DF4IAH/DL0WH_BiTuner/CAD/Eagle/Manufacturing/Pictures/HW_1V0/Bottom.png

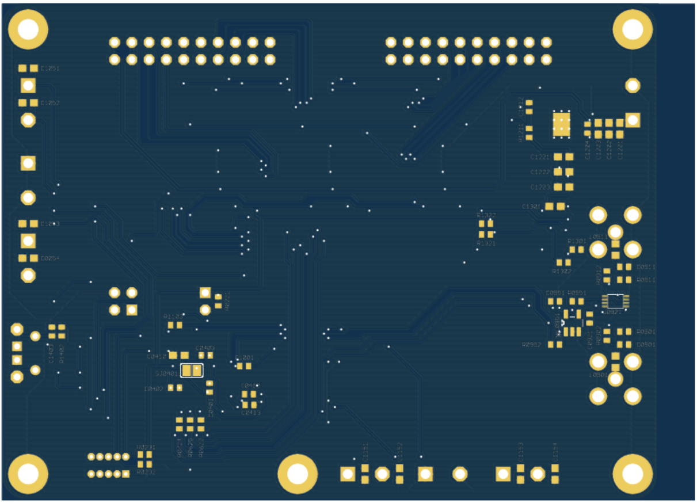
CAD/Eagle/Manufacturing/Pictures/HW_1V0/Bottom.png
