DF4IAH/DL0WH_BiTuner/CAD/Eagle/Manufacturing/Pictures/HW_1V0/Top_Silkscreen.png

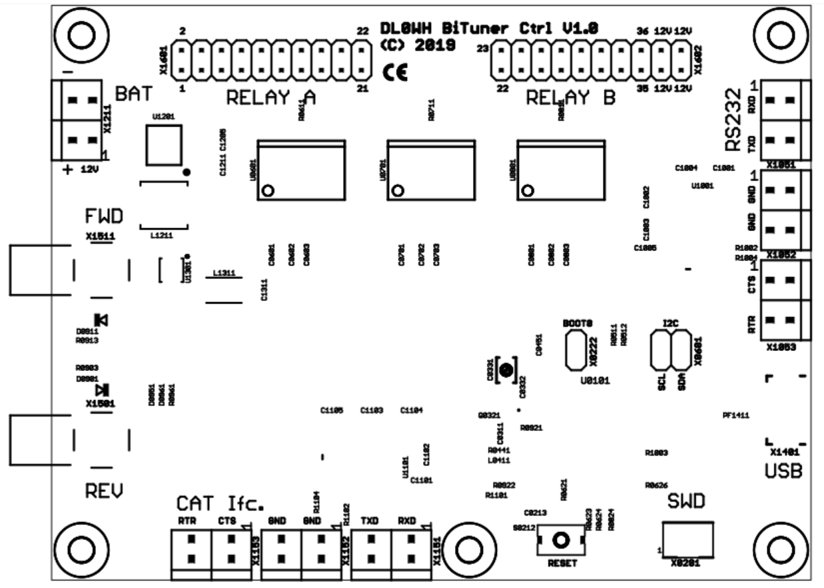
CAD/Eagle/Manufacturing/Pictures/HW_1V0/Top_Silkscreen.png
