DF4IAH/DL0WH_BiTuner/CAD/Eagle/Manufacturing/Pictures/HW_1V1/Bottom.png

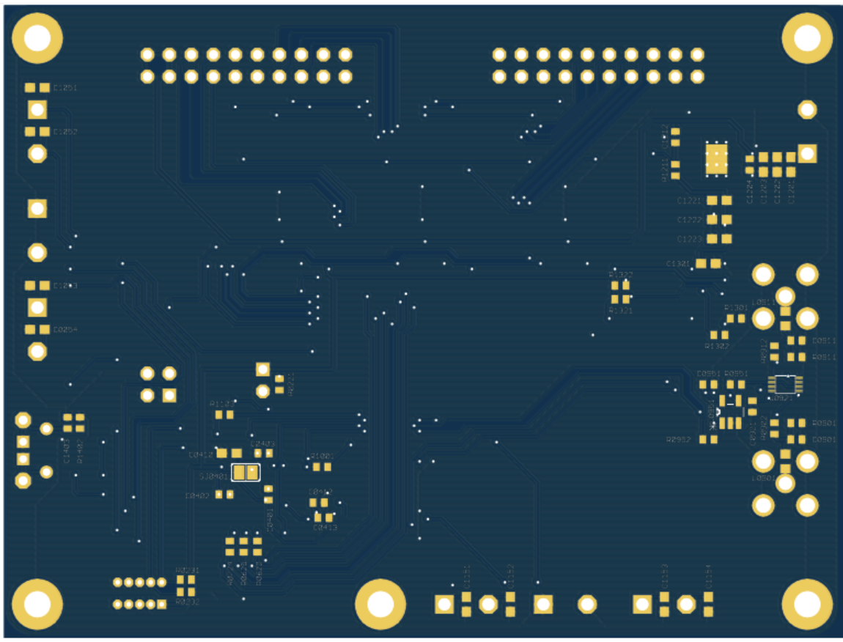
CAD/Eagle/Manufacturing/Pictures/HW_1V1/Bottom.png
