DF4IAH/DL0WH_BiTuner/CAD/Eagle/Manufacturing/Pictures/HW_1V1/Top.png

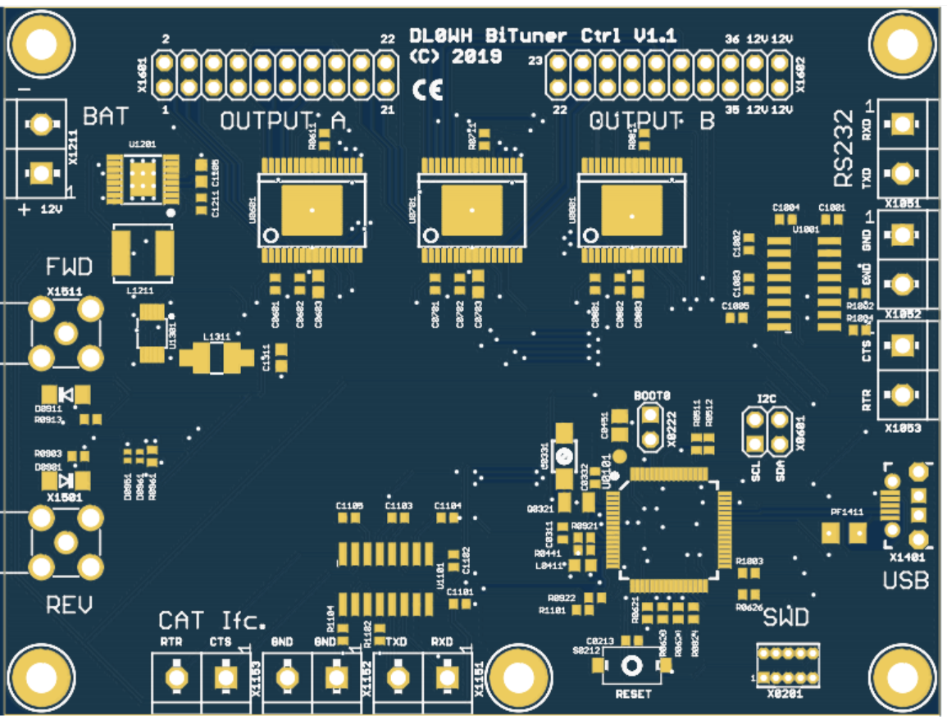
CAD/Eagle/Manufacturing/Pictures/HW_1V1/Top.png
