DF4IAH/DL0WH_BiTuner/Docs/09_Results/DL0WH_BiTuner_1V2_Rework_of_LogAmp/BiTuner_LogAmp__10C_30C_50C__1N43_2.png

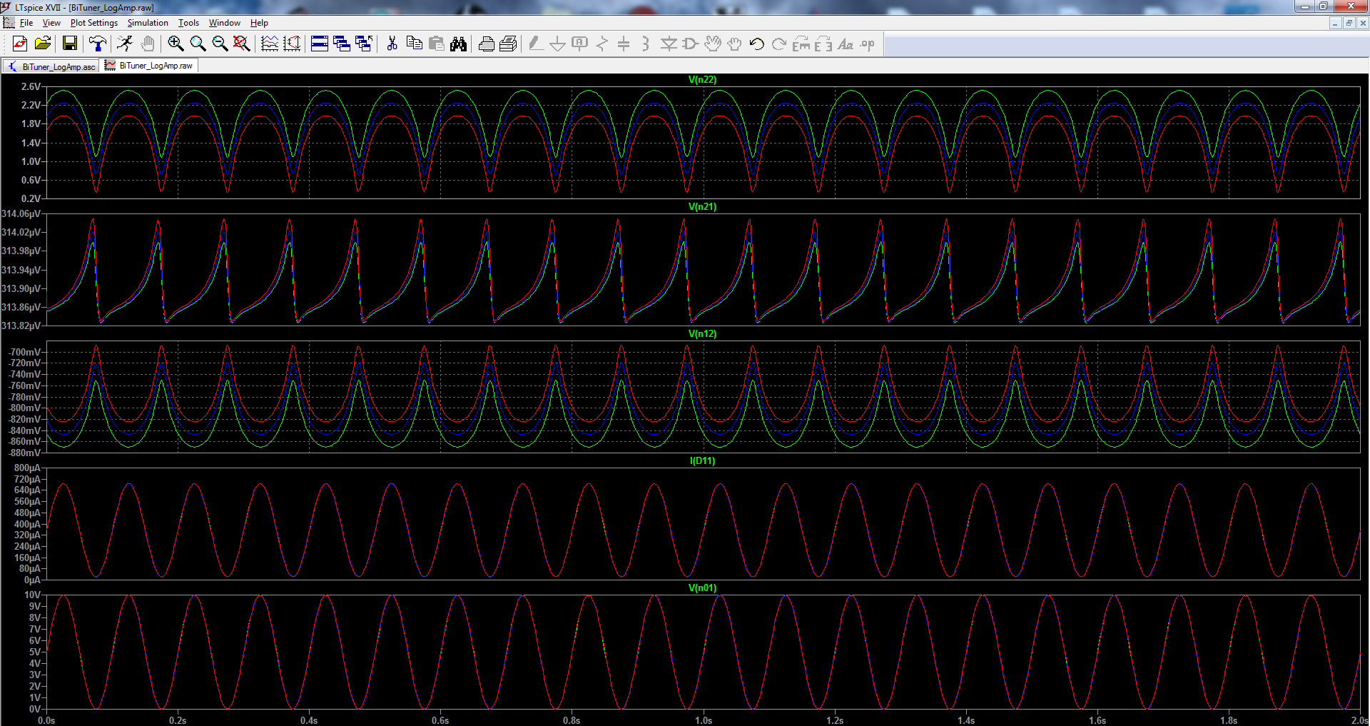
Docs/09_Results/DL0WH_BiTuner_1V2_Rework_of_LogAmp/BiTuner_LogAmp__10C_30C_50C__1N43_2.png
