DF4IAH/DL0WH_BiTuner/Docs/09_Results/Pictures/DL0WH_BiTuner_1V0_PCB_RoutingDone.png

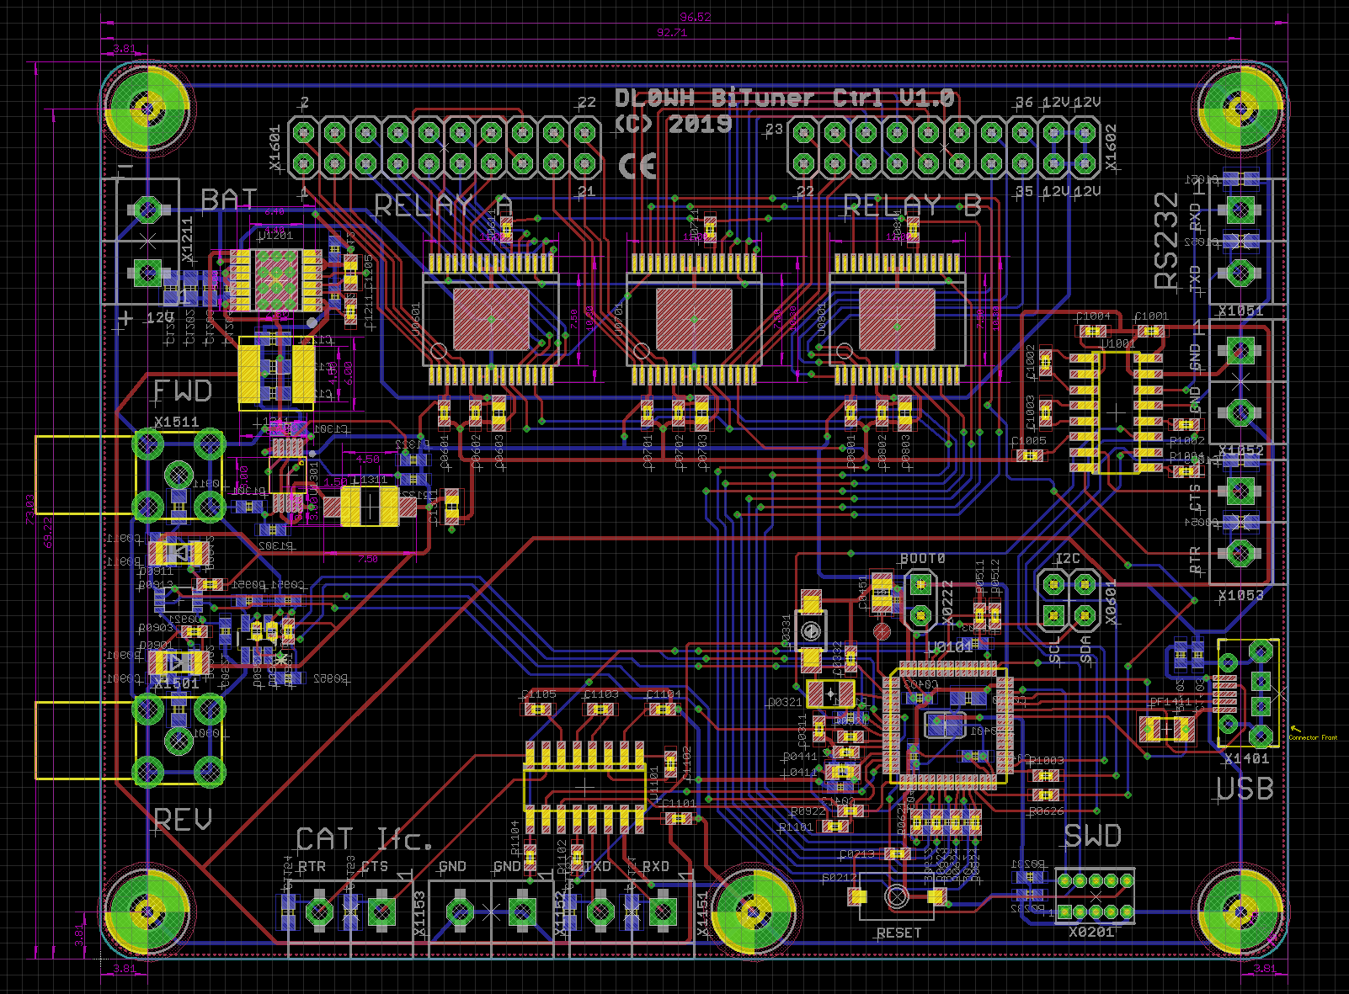
Docs/09_Results/Pictures/DL0WH_BiTuner_1V0_PCB_RoutingDone.png
