DF4IAH/DL0WH_BiTuner/Docs/09_Results/DL0WH_BiTuner_1V2_Rework_of_LogAmp/BiTuner_LogAmp.asc

C22: cap; 100pF
D11: diode; CMAD6001
R1: res; 150kR
R2: res; 2kR
R4: res; 1kR
R11: res; 15kR
R12: res; 1kR
R21: res; 5.3kR
R22: res; 20kR
U1: OPA354
U2: OPA354
V1: voltage; 3.3V
V2: voltage; 1.5V
V3: voltage; SINE(5 5 10)
Named nets: 0, n11, n12, n21, n22, nVp, nVm, n05, n01
.tran 0 2 0
*.step temp 10 50 20
.model CMAD6001 D( IS=70.1f RS=0.658 BV=75.0 IBV=500p CJO=2.00p M=0.333 N=1.24 TT=4.32u mfg=Central type=silicon )
