DF4IAH/DL0WH_BiTuner/Docs/09_Results/DL0WH_BiTuner_1V2_Rework_of_LogAmp/BiTuner_TempDiode.asc

D11: diode; CMAD6001
R1: res; 10kR
V1: voltage; 3.3V
Named nets: 0, nVp, nDa
.step temp 10 50 20
.tran 0 1 0
.model CMAD6001 D( IS=70.1f RS=0.658 BV=75.0 IBV=500p CJO=2.00p M=0.333 N=1.24 TT=4.32u mfg=Central type=silicon )
