DF4IAH/DL0WH_BiTuner/SW/_historic/DL0WH_BiTuner_Firmware/src/driver_init.c

/**
 * \file
 *
 * \brief Driver initialization.
 *
 (c) 2018 Microchip Technology Inc. and its subsidiaries.

    Subject to your compliance with these terms,you may use this software and
    any derivatives exclusively with Microchip products.It is your responsibility
    to comply with third party license terms applicable to your use of third party
    software (including open source software) that may accompany Microchip software.

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
    IN NO EVENT WILL MICROCHIP BE LIABLE FOR ANY INDIRECT, SPECIAL, PUNITIVE,
    INCIDENTAL OR CONSEQUENTIAL LOSS, DAMAGE, COST OR EXPENSE OF ANY KIND
    WHATSOEVER RELATED TO THE SOFTWARE, HOWEVER CAUSED, EVEN IF MICROCHIP HAS
    BEEN ADVISED OF THE POSSIBILITY OR THE DAMAGES ARE FORESEEABLE. TO THE
    FULLEST EXTENT ALLOWED BY LAW, MICROCHIP'S TOTAL LIABILITY ON ALL CLAIMS IN
    ANY WAY RELATED TO THIS SOFTWARE WILL NOT EXCEED THE AMOUNT OF FEES, IF ANY,
    THAT YOU HAVE PAID DIRECTLY TO MICROCHIP FOR THIS SOFTWARE.
 *
 */

/*
 * Code generated by START.
 *
 * This file will be overwritten when reconfiguring your START project.
 * Please copy examples or other code you want to keep to a separate file
 * to avoid losing it when reconfiguring.
 */

#include "driver_init.h"
#include <system.h>

void EXTERNAL_IRQ_0_initialization(void)
{

	EXTERNAL_IRQ_0_init();
}

/* Configure pins and initialize registers */
void ADC_0_initialization(void)
{

	ADC_0_init();
}

/* Configure pins and initialize registers */
void AC_0_initialization(void)
{

	AC_0_init();
}

/* configure pins and initialize registers */
void I2C_0_initialization(void)
{
	I2C_0_init();
}

/* configure the pins and initialize the registers */
void DAC_0_initialization(void)
{

	// Set pin direction to input
	PB4_set_dir(PORT_DIR_IN);

	PB4_set_pull_mode(
	    // <y> Pull configuration
	    // <id> pad_pull_config
	    // <PORT_PULL_OFF"> Off
	    // <PORT_PULL_UP"> Pull-up
	    PORT_PULL_OFF);

	// Set pin direction to output
	PB3_set_dir(PORT_DIR_OUT);

	PB3_set_level(
	    // <y> Initial level
	    // <id> pad_initial_level
	    // <false"> Low
	    // <true"> High
	    false);

	// Set pin direction to output
	PB5_set_dir(PORT_DIR_OUT);

	PB5_set_level(
	    // <y> Initial level
	    // <id> pad_initial_level
	    // <false"> Low
	    // <true"> High
	    false);

	DAC_0_init();
}

void PWM_0_initialization(void)
{

	PWM_0_init();
}

void PWM_1_initialization(void)
{

	PWM_1_init();
}

void TIMER_0_initialization(void)
{

	TIMER_0_init();
}

/* configure pins and initialize registers */
void USART_0_initialization(void)
{

	// Set pin direction to input
	PD0_set_dir(PORT_DIR_IN);

	PD0_set_pull_mode(
	    // <y> Pull configuration
	    // <id> pad_pull_config
	    // <PORT_PULL_OFF"> Off
	    // <PORT_PULL_UP"> Pull-up
	    PORT_PULL_OFF);

	// Set pin direction to output
	PD1_set_dir(PORT_DIR_OUT);

	PD1_set_level(
	    // <y> Initial level
	    // <id> pad_initial_level
	    // <false"> Low
	    // <true"> High
	    false);

	USART_0_init();
}

/**
 * \brief System initialization
 */
void system_init()
{
	mcu_init();

	sysctrl_init();

	FLASH_0_init();

	WDT_0_init();

	EXTERNAL_IRQ_0_initialization();

	//ADC_0_initialization();

	//AC_0_initialization();

	//I2C_0_initialization();

	//DAC_0_initialization();

	//PWM_0_initialization();

	//PWM_1_initialization();

	TIMER_0_initialization();

	/* GPIO init */
	{	
		//PORTB_set_port_dir(0xc0, PORT_DIR_IN);
		PORTB_set_port_dir(0x07, PORT_DIR_OUT);
		PORTB_write_port(0x00);

		//PORTC_set_port_dir(0xc0, PORT_DIR_IN);
		PORTC_set_port_dir(0x3f, PORT_DIR_OUT);
		PORTC_write_port(0x02);

		//PORTD_set_port_dir(0x01, PORT_DIR_IN);
		PORTD_set_port_dir(0xfc, PORT_DIR_OUT);
		PORTD_write_port(0x00);
	}

	USART_0_initialization();
}
