DF4IAH/DL0WH_BiTuner/SW/_Tests/prove.c

#include <stdio.h>
#include <string.h>
#include <stdlib.h>
#include <math.h>
#include "complex.h"

#include "prove.h"


extern float                g_adc_fwd_mv;
extern float                g_adc_swr;


static const float Controller_L0_nH                           = 50.0f;
static const float Controller_Ls_nH[8]                        = {
    187.5f,
    375.0f,
    750.0f,
    1.5e+3f,
    3.0e+3f,
    6.0e+3f,
    12.0e+3f,
    24.0e+3f
};

static const float Controller_C0_pF                           = 25.0f;
static float Controller_Cs_pF[8]                              = {
    25.0f,
    //33.0f,
    50.0f,
    89.0f,
    165.0f,
    340.0f,
    600.0f,
    1137.0f,
    1939.0f
};

static const float            Controller_AutoSWR_P_mW_Min       = 5.0f;
static const float            Controller_AutoSWR_P_mW_Max       = 15.0f;
static const float            Controller_AutoSWR_SWR_Max        = 1.1f;
static const float            Controller_AutoSWR_Time_ms_Max    = 750.0f;
static const uint8_t          Controller_AutoSWR_CVHpong_Max    = 3U;
static const uint8_t          Controller_AutoSWR_LCpong_Max     = 5U;
static uint32_t               s_controller_swr_tmr              = 0UL;
static uint32_t               s_controller_30ms_cnt             = 0UL;

static ControllerFsm_t        s_controller_FSM_state            = ControllerFsm__NOP;
static ControllerOptiCVH_t    s_controller_FSM_optiCVH          = ControllerOptiCVH__CV;
static ControllerOptiLC_t     s_controller_FSM_optiLC           = ControllerOptiLC__L;
static ControllerOptiStrat_t  s_controller_FSM_optiStrat        = ControllerOptiStrat__Double;
static ControllerOptiUpDn_t   s_controller_FSM_optiUpDn         = ControllerOptiUpDn__Up;
static uint8_t                s_controller_opti_CVHpongCtr      = 0U;
static uint8_t                s_controller_opti_LCpongCtr       = 0U;
static float                  s_controller_opti_min_swr         = 0.0f;
static float                  s_controller_opti_min_cand_swr    = 0.0f;
static float                  s_controller_opti_mid_swr         = 0.0f;
static float                  s_controller_opti_max_cand_swr    = 0.0f;
static float                  s_controller_opti_max_swr         = 0.0f;
static uint8_t                s_controller_opti_L               = 0U;
static float                  s_controller_opti_L_min_val       = 0.0f;
static float                  s_controller_opti_L_min_cand_val  = 0.0f;
static float                  s_controller_opti_L_mid_val       = 0.0f;
static float                  s_controller_opti_L_max_cand_val  = 0.0f;
static float                  s_controller_opti_L_max_val       = 0.0f;
static uint8_t                s_controller_opti_C               = 0U;
static float                  s_controller_opti_C_min_val       = 0.0f;
static float                  s_controller_opti_C_min_cand_val  = 0.0f;
static float                  s_controller_opti_C_mid_val       = 0.0f;
static float                  s_controller_opti_C_max_cand_val  = 0.0f;
static float                  s_controller_opti_C_max_val       = 0.0f;

static float                  s_controller_adc_fwd_mv           = 0.0f;
static float                  s_controller_adc_swr              = 0.0f;
static float                  s_controller_adc_fwd_mw           = 0.0f;
static float                  s_controller_last_swr             = 0.0f;

static _Bool                  s_controller_doCycle              = false;
static _Bool                  s_controller_doAdc                = false;



uint32_t controllerCalcMsgHdr(ControllerMsgDestinations_t dst, ControllerMsgDestinations_t src, uint8_t lengthBytes, uint8_t cmd)
{
  return ((uint32_t)dst << 24U) | ((uint32_t)src << 16U) | ((uint32_t)lengthBytes << 8U) | ((uint32_t)cmd);
}

uint32_t controllerCalcMsgInit(uint32_t* ary, ControllerMsgDestinations_t dst, uint32_t startDelayMs)
{
  ary[0] = 0; // controllerCalcMsgHdr(dst, Destinations__Controller, sizeof(uint32_t), MsgController__InitDo);
  ary[1] = startDelayMs;
  return 2UL;
}


/* Calculation function */

float controllerCalcMatcherL2nH(uint8_t Lval)
{
  float sum = Controller_L0_nH;

  for (uint8_t idx = 0; idx < 8; idx++) {
    if (Lval & (1U << idx)) {
      sum += Controller_Ls_nH[idx];
    }
  }
  return sum;
}

float controllerCalcMatcherC2pF(uint8_t Cval)
{
  float sum = Controller_C0_pF;

  for (uint8_t idx = 0; idx < 8; idx++) {
    if (Cval & (1U << idx)) {
      sum += Controller_Cs_pF[idx];
    }
  }
  return sum;
}

uint8_t controllerCalcMatcherNH2L(float nH)
{
  float   absMin  = 1e+3f;
  uint8_t valThis = 0U;

  for (uint16_t val = 0U; val < 256U; val++) {
    const float valL    = controllerCalcMatcherL2nH(val);
    const float absThis = fabs(valL - nH);

    if (absMin > absThis) {
      absMin  = absThis;
      valThis = val;
    }
  }
  return valThis;
}

uint8_t controllerCalcMatcherPF2C(float pF)
{
  float   absMin  = 1e+3f;
  uint8_t valThis = 0U;

  for (uint16_t val = 0U; val < 256U; val++) {
    const float valC    = controllerCalcMatcherC2pF(val);
    const float absThis = fabs(valC - pF);

    if (absMin > absThis) {
      absMin  = absThis;
      valThis = val;
    }
  }
  return valThis;
}

float controllerCalcVSWR_Simu(float antOhmR, float antOhmI, float Z0R, float Z0I, float frequencyHz)
{
  const float Z0abs = sqrtf(Z0R * Z0R + Z0I * Z0I);
  const float omega = (float) (2.0 * M_PI * frequencyHz);
  float L_nH        = s_controller_opti_L_mid_val;
  float C_pF        = s_controller_opti_C_mid_val;
  float outR        = antOhmR;
  float outX        = antOhmI;
  float gammaRe     = 0.0f;
  float gammaIm     = 0.0f;
  float gammaAbs    = 0.0f;
  float gammaPhi    = 0.0f;
  float vswr        = 99.0f;

  /* For security only */
  if (L_nH < 1.0f) {
    L_nH = Controller_L0_nH;
  }
  if (C_pF < 1.0f) {
    C_pF = Controller_C0_pF;
  }

  if (s_controller_FSM_optiCVH == ControllerOptiCVH__CV) {
    /* Inductivity at the antenna */

    /* Serial structure */
    float LOhmX = omega * (L_nH * 1e-9f);
    outX += LOhmX;

    /* Parallel structure */
    {
      /* Invert to admitance */
      float outG = 0.0f;
      float outY = 0.0f;
      cInv(&outG, &outY, outR, outX);

      /* Capacity */
      const float COhmX = -1.0f / (omega * (C_pF * 1e-12f));
      float CSimG = 0.0f;
      float CSimY = 0.0f;
      cInv(&CSimG, &CSimY, 0.0f, COhmX);

      /* Adding C parallel to the circuit */
      outY += CSimY;

      /* Revert to impedance */
      cInv(&outR, &outX, outG, outY);
    }

  } else {
    /* Capacity at the antenna */

    /* Parallel structure */
    {
      /* Invert to admitance */
      float outG = 0.0f;
      float outY = 0.0f;
      cInv(&outG, &outY, outR, outX);

      /* Capacity */
      const float COhmX = -1.0f / (omega * (C_pF * 1e-12f));
      float CSimG = 0.0f;
      float CSimY = 0.0f;
      cInv(&CSimG, &CSimY, 0.0f, COhmX);

      /* Adding C parallel to the circuit */
      outY += CSimY;

      /* Revert to impedance */
      cInv(&outR, &outX, outG, outY);
    }

    /* Serial structure */
    float LOhmX = omega * (L_nH * 1e-9f);
    outX += LOhmX;
  }

  /* Log impedance at the transceiver */
  {
    char      buf[256];
    int32_t   trxRi, trxXi;
    uint32_t  trxRf, trxXf;

    mainCalcFloat2IntFrac(outR, 3U, &trxRi, &trxRf);
    mainCalcFloat2IntFrac(outX, 3U, &trxXi, &trxXf);

    int len = sprintf(buf,
        "VSWR_Simu: Resulting Impedance at the transceiver Z= R (%3d.%03u Ohm) + jX (%3d.%03u Ohm)\t\t having L=%5d nH and C=%5d pF, ",
        trxRi, trxRf,  trxXi, trxXf,  (uint32_t)L_nH, (uint32_t)C_pF);

    usbLogLen(buf, len);
  }

  /* Calculate Gamma = (Z - 1) / (Z + 1) */
  {
    /* Normalized Impedance */
    float outRnorm = outR / Z0abs;
    float outXnorm = outX / Z0abs;

    cDiv(&gammaRe, &gammaIm, (outRnorm - 1.0f), outXnorm, (outRnorm + 1.0f), outXnorm);

    gammaAbs = sqrtf(gammaRe * gammaRe  +  gammaIm * gammaIm);
    gammaPhi = (float) ((180.0 / M_PI) * atan2(gammaIm, gammaRe));
  }

  /* Log reflection coefficient at the transceiver */
  {
    char      buf[256];
    int32_t   gammaAbsi, gammaPhii, gammaRei, gammaImi;
    uint32_t  gammaAbsf, gammaPhif, gammaRef, gammaImf;

    mainCalcFloat2IntFrac(gammaAbs, 3U, &gammaAbsi, &gammaAbsf);
    mainCalcFloat2IntFrac(gammaPhi, 3U, &gammaPhii, &gammaPhif);
    mainCalcFloat2IntFrac(gammaRe,  3U, &gammaRei,  &gammaRef);
    mainCalcFloat2IntFrac(gammaIm,  3U, &gammaImi,  &gammaImf);

    int len = sprintf(buf,
        "|Gamma|= %1d.%03u,  Phi(Gamma)= %3d.%03u having Re(Gamma)= %3d.%03u, Im(Gamma)= %3d.%03u, ",
        gammaAbsi, gammaAbsf,  gammaPhii, gammaPhif,  gammaRei, gammaRef,  gammaImi, gammaImf);

    usbLogLen(buf, len);
  }

  /* Calculate VSWR = (1 + GammaAbs) / (1 - GammaAbs) */
  if (gammaAbs < 0.99f) {
    vswr = (1.0f + gammaAbs) / (1.0f - gammaAbs);

  } else {
    vswr = 99.9f;
  }

  /* Log reflection coefficient at the transceiver */
  {
    char buf[128];
    int32_t   vswri;
    uint32_t  vswrf;

    mainCalcFloat2IntFrac(vswr, 3U, &vswri, &vswrf);

    int len = sprintf(buf,
        "VSWR= %d.%03u.\r\n\r\n",
        vswri, vswrf);

    usbLogLen(buf, len);
  }

  return vswr;
}


/* FSM functions */

static void controllerFSM_LogAutoFinished(void)
{
  /* SWR: we have got it */

  s_controller_FSM_state = ControllerFsm__done;
  s_controller_doAdc     = true;

  /* Logging */
  {
    char buf[128];

    const int len = sprintf(buf, "Controller FSM: ControllerFsm__findImagZeroL - SWR good enough - tuner has finished.\r\n");
    usbLogLen(buf, len);
  }
}

static void controllerFSM_LogState(void)
{
  /* Show current state of optimization */
  char      buf[512];

  int32_t   s_controller_opti_L_min_val_i;
  uint32_t  s_controller_opti_L_min_val_f;

  int32_t   s_controller_opti_L_min_cand_val_i;
  uint32_t  s_controller_opti_L_min_cand_val_f;

  int32_t   s_controller_opti_L_mid_val_i;
  uint32_t  s_controller_opti_L_mid_val_f;

  int32_t   s_controller_opti_L_max_cand_val_i;
  uint32_t  s_controller_opti_L_max_cand_val_f;

  int32_t   s_controller_opti_L_max_val_i;
  uint32_t  s_controller_opti_L_max_val_f;


  int32_t   s_controller_opti_C_min_val_i;
  uint32_t  s_controller_opti_C_min_val_f;

  int32_t   s_controller_opti_C_min_cand_val_i;
  uint32_t  s_controller_opti_C_min_cand_val_f;

  int32_t   s_controller_opti_C_mid_val_i;
  uint32_t  s_controller_opti_C_mid_val_f;

  int32_t   s_controller_opti_C_max_cand_val_i;
  uint32_t  s_controller_opti_C_max_cand_val_f;

  int32_t   s_controller_opti_C_max_val_i;
  uint32_t  s_controller_opti_C_max_val_f;

  int       len;

  s_controller_30ms_cnt += 30UL;

  len = sprintf(buf,
                "Controller FSM:\tcontrollerFSM_LogState - time= %6d ms - FSM_state= %u, FSM_optiLC= %u, FSM_optiUpDn= %u, FSM_optiVCH= %u, FSM_opti_L= %03u, FSM_opti_C= %03u,\r\n" \
                "\t\t\topti_CVHpongCtr= %03u, opti_LCpongCtr= %03u,\r\n",
                s_controller_30ms_cnt,
                s_controller_FSM_state,       s_controller_FSM_optiLC, s_controller_FSM_optiUpDn, s_controller_FSM_optiCVH, s_controller_opti_L, s_controller_opti_C,
                s_controller_opti_CVHpongCtr, s_controller_opti_LCpongCtr);
  usbLogLen(buf, len);

  mainCalcFloat2IntFrac(s_controller_opti_L_min_val,      1, &s_controller_opti_L_min_val_i,      &s_controller_opti_L_min_val_f     );
  mainCalcFloat2IntFrac(s_controller_opti_L_min_cand_val, 1, &s_controller_opti_L_min_cand_val_i, &s_controller_opti_L_min_cand_val_f);
  mainCalcFloat2IntFrac(s_controller_opti_L_mid_val,      1, &s_controller_opti_L_mid_val_i,      &s_controller_opti_L_mid_val_f     );
  mainCalcFloat2IntFrac(s_controller_opti_L_max_cand_val, 1, &s_controller_opti_L_max_cand_val_i, &s_controller_opti_L_max_cand_val_f);
  mainCalcFloat2IntFrac(s_controller_opti_L_max_val,      1, &s_controller_opti_L_max_val_i,      &s_controller_opti_L_max_val_f     );

  mainCalcFloat2IntFrac(s_controller_opti_C_min_val,      1, &s_controller_opti_C_min_val_i,      &s_controller_opti_C_min_val_f     );
  mainCalcFloat2IntFrac(s_controller_opti_C_min_cand_val, 1, &s_controller_opti_C_min_cand_val_i, &s_controller_opti_C_min_cand_val_f);
  mainCalcFloat2IntFrac(s_controller_opti_C_mid_val,      1, &s_controller_opti_C_mid_val_i,      &s_controller_opti_C_mid_val_f     );
  mainCalcFloat2IntFrac(s_controller_opti_C_max_cand_val, 1, &s_controller_opti_C_max_cand_val_i, &s_controller_opti_C_max_cand_val_f);
  mainCalcFloat2IntFrac(s_controller_opti_C_max_val,      1, &s_controller_opti_C_max_val_i,      &s_controller_opti_C_max_val_f     );
  len = sprintf(buf,
                "\t\t\tL_min= %5d.%01u nH, L_min_c= %5d.%01u nH, L_mid= %5d.%01u nH, L_max_c= %5d.%01u nH, L_max= %5d.%01u nH,\r\n",
                s_controller_opti_L_min_val_i,      s_controller_opti_L_min_val_f,
                s_controller_opti_L_min_cand_val_i, s_controller_opti_L_min_cand_val_f,
                s_controller_opti_L_mid_val_i,      s_controller_opti_L_mid_val_f,
                s_controller_opti_L_max_cand_val_i, s_controller_opti_L_max_cand_val_f,
                s_controller_opti_L_max_val_i,      s_controller_opti_L_max_val_f
               );
  usbLogLen(buf, len);


  len = sprintf(buf,
                "\t\t\tC_min= %5d.%01u pF, C_min_c= %5d.%01u pF, C_mid= %5d.%01u pF, C_max_c= %5d.%01u pF, C_max= %5d.%01u pF,\r\n",
                s_controller_opti_C_min_val_i,      s_controller_opti_C_min_val_f,
                s_controller_opti_C_min_cand_val_i, s_controller_opti_C_min_cand_val_f,
                s_controller_opti_C_mid_val_i,      s_controller_opti_C_mid_val_f,
                s_controller_opti_C_max_cand_val_i, s_controller_opti_C_max_cand_val_f,
                s_controller_opti_C_max_val_i,      s_controller_opti_C_max_val_f
               );
  usbLogLen(buf, len);


  int32_t   swr_i, last_swr_i;
  uint32_t  swr_f, last_swr_f;

  mainCalcFloat2IntFrac(s_controller_adc_swr,  3, &swr_i,      &swr_f);
  mainCalcFloat2IntFrac(s_controller_last_swr, 3, &last_swr_i, &last_swr_f);
  len = sprintf(buf,
                "\t\t\tfwd_mv=%5u mV, fwd_mw=%5u mW,\r\n" \
                "\t\t\tswr=%5d.%03u, last_swr=%5d.%03u.\r\n\r\n",
                (uint32_t)s_controller_adc_fwd_mv, (uint32_t)s_controller_adc_fwd_mw,
                swr_i, swr_f, last_swr_i, last_swr_f);
  usbLogLen(buf, len);
}

static void controllerFSM_GetGlobalVars(void)
{
  s_controller_last_swr       = s_controller_adc_swr;

  __disable_irq();
  s_controller_adc_fwd_mv     = g_adc_fwd_mv;
  s_controller_adc_swr        = g_adc_swr;
  __enable_irq();

  s_controller_opti_mid_swr   = s_controller_adc_swr;
  s_controller_adc_fwd_mw     = mainCalc_mV_to_mW(s_controller_adc_fwd_mv);
  printf("controllerFSM_GetGlobalVars: s_controller_adc_fwd_mv= %.3f mV, s_controller_adc_fwd_mw= %.3f mW, s_controller_adc_swr= %.3f\r\n",
          s_controller_adc_fwd_mv, s_controller_adc_fwd_mw, s_controller_adc_swr);
}

static void controllerFSM_PushOptiVars(void)
{
  uint8_t controller_opti_CV;
  uint8_t controller_opti_CH;
  uint32_t msgAry[2];

  /* Calculate current L and C counter setings */
  s_controller_opti_L = controllerCalcMatcherNH2L(s_controller_opti_L_mid_val);
  s_controller_opti_C = controllerCalcMatcherPF2C(s_controller_opti_C_mid_val);

  /* Update CV/CH state */
  if (s_controller_FSM_optiCVH == ControllerOptiCVH__CH) {
    controller_opti_CV  = 0U;
    controller_opti_CH  = 1U;

  } else {
    controller_opti_CV  = 1U;
    controller_opti_CH  = 0U;
  }

  /* Compose relay bitmap */
  msgAry[1] = ((uint32_t)  controller_opti_CH << 17) |
              ((uint32_t)  controller_opti_CV << 16) |
              ((uint32_t)s_controller_opti_L  <<  8) |
              ((uint32_t)s_controller_opti_C       ) ;

  /* Three extra bytes to take over */
  msgAry[0] = controllerCalcMsgHdr(Destinations__Rtos_Default, Destinations__Controller, 3, MsgDefault__SetVar03_C_L_CV_CH);
  //controllerMsgPushToOutQueue(sizeof(msgAry) / sizeof(uint32_t), msgAry, osWaitForever);
}

static void controllerFSM_StartAdc(void)
{
  s_controller_doAdc = true;
}

static _Bool controllerFSM_CheckPower(void)
{
  if ((Controller_AutoSWR_P_mW_Min > s_controller_adc_fwd_mw) || (s_controller_adc_fwd_mw > Controller_AutoSWR_P_mW_Max)) {
    /* Logging */
    {
      char      buf[128];
      int32_t   pwr_i;
      uint32_t  pwr_f;

      mainCalcFloat2IntFrac(s_controller_adc_fwd_mw, 3, &pwr_i, &pwr_f);
      const int len = sprintf(buf,
                              "Controller FSM: power=%5d.%03u out of [%u .. %u] Watts - stop auto tuner.\r\n",
                              pwr_i, pwr_f,
                              (uint16_t)Controller_AutoSWR_P_mW_Min, (uint16_t)Controller_AutoSWR_P_mW_Max);
      usbLogLen(buf, len);
    }

    /* Reset SWR start timer */
    s_controller_swr_tmr = osKernelSysTick();

    /* Overdrive or to low energy */
    s_controller_FSM_state = ControllerFsm__doAdc;

    return true;
  }
  return false;
}

static _Bool controllerFSM_CheckSwrTime(void)
{
  if (s_controller_opti_mid_swr < Controller_AutoSWR_SWR_Max) {
    /* Logging */
    {
      char buf[128];
      int32_t   swr_i;
      uint32_t  swr_f;

      mainCalcFloat2IntFrac(s_controller_adc_swr, 3, &swr_i, &swr_f);
      const int len = sprintf(buf,
                              "Controller FSM: SWR= %2d.%03u is good enough - stop auto tuner.\r\n",
                              swr_i, swr_f);
      usbLogLen(buf, len);
    }

    /* No need to start */
    s_controller_FSM_state = ControllerFsm__doAdc;

    return true;

  } else if (Controller_AutoSWR_Time_ms_Max > (osKernelSysTick() - s_controller_swr_tmr)) {
    /* Timer has not yet elapsed */
    s_controller_FSM_state = ControllerFsm__doAdc;

    return true;
  }
  return false;
}

#if 0
static void ControllerFSM_HandleLimits(_Bool swrGotBetter)
{
  if (swrGotBetter) {
    /* SWR got better */

    if (s_controller_FSM_optiUpDn == ControllerOptiUpDn__Up) {
      /* Increasing */
      printf("ControllerFSM_HandleLimits(Better) 1: Up\r\n");

      s_controller_opti_min_swr        = s_controller_opti_min_cand_swr;
      s_controller_opti_min_cand_swr   = s_controller_opti_mid_swr;
        
      if (s_controller_FSM_optiLC == ControllerOptiLC__L) {
        /* Inductance at least this value */
        s_controller_opti_L_min_val      = s_controller_opti_L_min_cand_val;
        s_controller_opti_L_min_cand_val = s_controller_opti_L_mid_val;

        /* Push max ahead */
        s_controller_opti_L_max_val      = s_controller_opti_L_max_cand_val = s_controller_opti_L_mid_val;
        s_controller_opti_max_swr        = s_controller_opti_max_cand_swr   = s_controller_opti_mid_swr;

      } else {
        /* Capacitance at least this value */
        s_controller_opti_C_min_val      = s_controller_opti_C_min_cand_val;
        s_controller_opti_C_min_cand_val = s_controller_opti_C_mid_val;

        /* Push max ahead */
        s_controller_opti_C_max_val      = s_controller_opti_C_max_cand_val = s_controller_opti_C_mid_val;
        s_controller_opti_max_swr        = s_controller_opti_max_cand_swr   = s_controller_opti_mid_swr;
      }

    } else {
      /* Decreasing */
      printf("ControllerFSM_HandleLimits(Better) 2: Down\r\n");

      s_controller_opti_max_swr        = s_controller_opti_max_cand_swr;
      s_controller_opti_max_cand_swr   = s_controller_opti_mid_swr;

      if (s_controller_FSM_optiLC == ControllerOptiLC__L) {
        /* Inductance at most this value */
        s_controller_opti_L_max_val      = s_controller_opti_L_max_cand_val;
        s_controller_opti_L_max_cand_val = s_controller_opti_L_mid_val;

        /* Push min ahead */
        s_controller_opti_L_min_val      = s_controller_opti_L_min_cand_val = s_controller_opti_L_mid_val;
        s_controller_opti_min_swr        = s_controller_opti_min_cand_swr   = s_controller_opti_mid_swr;

      } else {
        /* Capacitance at most this value */
        s_controller_opti_C_max_val      = s_controller_opti_C_max_cand_val;
        s_controller_opti_C_max_cand_val = s_controller_opti_C_mid_val;

        /* Push min ahead */
        s_controller_opti_C_min_val      = s_controller_opti_C_min_cand_val = s_controller_opti_C_mid_val;
        s_controller_opti_min_swr        = s_controller_opti_min_cand_swr   = s_controller_opti_mid_swr;
      }
    }

  } else {
    /* SWR got worse */

    if (s_controller_FSM_optiUpDn == ControllerOptiUpDn__Up) {
      /* Increasing */

      if (s_controller_FSM_optiLC == ControllerOptiLC__L) {
        /* Inductance at most this value */
        s_controller_opti_L_max_val      = s_controller_opti_L_max_cand_val = s_controller_opti_L_mid_val;
        s_controller_opti_max_swr        = s_controller_opti_max_cand_swr   = s_controller_opti_mid_swr;

      } else {
        /* Capacitance at most this value */
        s_controller_opti_C_max_val      = s_controller_opti_C_max_cand_val = s_controller_opti_C_mid_val;
        s_controller_opti_max_swr        = s_controller_opti_max_cand_swr   = s_controller_opti_mid_swr;
      }

    } else {
      /* Decreasing */

      if (s_controller_FSM_optiLC == ControllerOptiLC__L) {
        /* Inductance at least this value */
        s_controller_opti_L_min_val      = s_controller_opti_L_min_cand_val = s_controller_opti_L_mid_val;
        s_controller_opti_min_swr        = s_controller_opti_min_cand_swr   = s_controller_opti_mid_swr;

      } else {
        /* Capacitance at least this value */
        s_controller_opti_C_min_val      = s_controller_opti_C_min_cand_val = s_controller_opti_C_mid_val;
        s_controller_opti_min_swr        = s_controller_opti_min_cand_swr   = s_controller_opti_mid_swr;
      }
    }
  }
}
#endif

static void controllerFSM_SwitchOverCVH(void)
{
  /* Check if another CVH switch over is allowed */
  if (++s_controller_opti_CVHpongCtr <= Controller_AutoSWR_CVHpong_Max) {
    s_controller_opti_LCpongCtr = 0U;

    /* Logging */
    {
      char      buf[128];
      const int len = sprintf(buf,
                              "Controller FSM: switch over the constellation to %d (0: CV, 1: CH), CVH pingpong ctr=%u.\r\n",
                              !s_controller_FSM_optiCVH, s_controller_opti_CVHpongCtr);
      usbLogLen(buf, len);
    }

    /* Switch over to opposite CVH constellation */
    s_controller_FSM_optiCVH = !s_controller_FSM_optiCVH;
    if (s_controller_FSM_optiCVH == ControllerOptiCVH__CH) {
      s_controller_FSM_optiLC     = ControllerOptiLC__C;
      s_controller_FSM_optiStrat  = ControllerOptiStrat__Double;
      s_controller_FSM_optiUpDn   = ControllerOptiUpDn__Up;
      s_controller_opti_L_min_val = s_controller_opti_L_min_cand_val = s_controller_opti_L_mid_val = Controller_L0_nH;
      s_controller_opti_C_min_val = s_controller_opti_C_min_cand_val = Controller_C0_pF;
      s_controller_opti_C_mid_val = Controller_C0_pF + Controller_Cs_pF[0];
      s_controller_opti_min_swr   = s_controller_opti_min_cand_swr   = s_controller_adc_swr        = 99.9f;
      s_controller_FSM_state      = ControllerFsm__findImagZero;

    } else {
      s_controller_FSM_optiLC     = ControllerOptiLC__L;
      s_controller_FSM_optiStrat  = ControllerOptiStrat__Double;
      s_controller_FSM_optiUpDn   = ControllerOptiUpDn__Up;
      s_controller_opti_C_min_val = s_controller_opti_C_min_cand_val = s_controller_opti_C_mid_val = Controller_C0_pF;
      s_controller_opti_L_min_val = s_controller_opti_L_min_cand_val = Controller_L0_nH;
      s_controller_opti_L_mid_val = Controller_L0_nH + Controller_Ls_nH[0];
      s_controller_opti_min_swr   = s_controller_opti_min_cand_swr   = s_controller_adc_swr        = 99.9f;
      s_controller_FSM_state      = ControllerFsm__findImagZero;
    }

    s_controller_FSM_optiStrat    = ControllerOptiStrat__Double;

  } else {
    /* Exhausted - start over again */
    s_controller_FSM_state = ControllerFsm__doAdc;
  }
}

static void controllerFSM_DoubleStrategy(void)
{
  if (s_controller_FSM_optiLC == ControllerOptiLC__L) {
    /* Double L */
    s_controller_opti_L_mid_val *= 2.0f;

    if (s_controller_opti_L_max_cand_val < s_controller_opti_L_mid_val) {
      s_controller_opti_L_max_cand_val   = s_controller_opti_L_mid_val;
      s_controller_opti_max_cand_swr     = s_controller_opti_mid_swr;
    }

    if (s_controller_opti_L_max_val      < s_controller_opti_L_mid_val) {
      s_controller_opti_L_max_val        = s_controller_opti_L_mid_val;
      s_controller_opti_max_swr          = s_controller_opti_mid_swr;
    }

    s_controller_opti_L_min_val          = s_controller_opti_L_min_cand_val;
    s_controller_opti_L_min_cand_val     = s_controller_opti_L_mid_val;

  } else {
    /* Double C */
    s_controller_opti_C_mid_val *= 2.0f;

    if (s_controller_opti_C_max_cand_val < s_controller_opti_C_mid_val) {
      s_controller_opti_C_max_cand_val   = s_controller_opti_C_mid_val;
      s_controller_opti_max_cand_swr     = s_controller_opti_mid_swr;
    }

    if (s_controller_opti_C_max_val      < s_controller_opti_C_mid_val) {
      s_controller_opti_C_max_val        = s_controller_opti_C_mid_val;
      s_controller_opti_max_swr          = s_controller_opti_mid_swr;
    }

    s_controller_opti_C_min_val          = s_controller_opti_C_min_cand_val;
    s_controller_opti_C_min_cand_val     = s_controller_opti_C_mid_val;
  }

  s_controller_opti_min_swr            = s_controller_opti_min_cand_swr;
  s_controller_opti_min_cand_swr       = s_controller_opti_mid_swr;
}

static void controllerFSM_HalfStrategy(void)
{
  /* Direction */
  if (s_controller_FSM_optiUpDn == ControllerOptiUpDn__Dn) {
    /* Down */
    printf("controllerFSM_HalfStrategy 1: Down\r\n");

    if ((s_controller_opti_min_swr <  s_controller_opti_mid_swr) ||
        (s_controller_opti_mid_swr <= s_controller_opti_max_swr)) {
      /* Lower limit is better */
      //s_controller_FSM_optiUpDn        = ControllerOptiUpDn__Dn;
      printf("controllerFSM_HalfStrategy 1a: min= %.0fnH | %.0fpF swr(min)= %.3f better than mid= %.0fnH | %.0fpH swr(mid)= %.3f\r\n", s_controller_opti_L_min_val, s_controller_opti_C_min_val, s_controller_opti_min_swr, s_controller_opti_L_mid_val, s_controller_opti_C_mid_val, s_controller_opti_mid_swr);

      /* Move mid --> max_cand --> max */
      s_controller_opti_max_swr          = s_controller_opti_max_cand_swr;
      s_controller_opti_max_cand_swr     = s_controller_opti_mid_swr;

      if (s_controller_FSM_optiLC == ControllerOptiLC__L) {
        /* Find intermediate L */
        s_controller_opti_L_max_val      = s_controller_opti_L_max_cand_val;
        s_controller_opti_L_max_cand_val = s_controller_opti_L_mid_val;

        /* New mid */
        s_controller_opti_L_mid_val      = (s_controller_opti_L_min_val + s_controller_opti_L_max_cand_val) / 2.0f;

      } else {
        /* Find intermediate C */
        s_controller_opti_C_max_val      = s_controller_opti_C_max_cand_val;
        s_controller_opti_C_max_cand_val = s_controller_opti_C_mid_val;

        /* New mid */
        s_controller_opti_C_mid_val      = (s_controller_opti_C_min_val + s_controller_opti_C_max_cand_val) / 2.0f;
      }

    } else {
      /* Upper limit is better */
      s_controller_FSM_optiUpDn = ControllerOptiUpDn__Up;
      printf("controllerFSM_HalfStrategy 1b: max= %.0fnH | %.0fpF swr(max)= %.3f better than mid= %.0fnH | %.0fpF swr(mid)= %.3f\r\n", s_controller_opti_L_max_val, s_controller_opti_C_max_val, s_controller_opti_max_swr, s_controller_opti_L_mid_val, s_controller_opti_C_mid_val, s_controller_opti_mid_swr);

      /* Replace min, min_cand by mid */
      s_controller_opti_min_swr          = s_controller_opti_min_cand_swr    = s_controller_opti_mid_swr;

      if (s_controller_FSM_optiLC == ControllerOptiLC__L) {
        /* Find intermediate L */
        s_controller_opti_L_min_val      = s_controller_opti_L_min_cand_val  = s_controller_opti_L_mid_val;
 
        /* New mid */
        s_controller_opti_L_mid_val      = (s_controller_opti_L_mid_val + s_controller_opti_L_max_val) / 2.0f;

      } else {
        /* Find intermediate C */
        s_controller_opti_C_min_val      = s_controller_opti_C_min_cand_val  = s_controller_opti_L_mid_val;
 
        /* New mid */
        s_controller_opti_C_mid_val      = (s_controller_opti_C_mid_val + s_controller_opti_C_max_val) / 2.0f;
      }
    }

  } else {
    /* Up */
    printf("controllerFSM_HalfStrategy 2: Up\r\n");

    if (s_controller_opti_mid_swr < s_controller_opti_min_cand_swr) {
      /* Upper limit is better */
      //s_controller_FSM_optiUpDn        = ControllerOptiUpDn__Up;

      /* Move mid --> min_cand --> min */
      s_controller_opti_min_swr          = s_controller_opti_min_cand_swr;
      s_controller_opti_min_cand_swr     = s_controller_opti_mid_swr;

      if (s_controller_FSM_optiLC == ControllerOptiLC__L) {
        /* Find intermediate L */
        s_controller_opti_L_min_val      = s_controller_opti_L_min_cand_val;
        s_controller_opti_L_min_cand_val = s_controller_opti_L_mid_val;

        /* New mid */
        s_controller_opti_L_mid_val      = (s_controller_opti_L_min_cand_val + s_controller_opti_L_max_val) / 2.0f;

      } else {
        /* Find intermediate C */
        s_controller_opti_C_min_val      = s_controller_opti_C_min_cand_val;
        s_controller_opti_C_min_cand_val = s_controller_opti_C_mid_val;

        /* New mid */
        s_controller_opti_C_mid_val      = (s_controller_opti_C_min_cand_val + s_controller_opti_C_max_val) / 2.0f;
      }

    } else {
      /* Lower limit is better */
      s_controller_FSM_optiUpDn          = ControllerOptiUpDn__Dn;

      /* Replace max, max_cand by mid */
      s_controller_opti_max_swr          = s_controller_opti_max_cand_swr    = s_controller_opti_mid_swr;

      if (s_controller_FSM_optiLC == ControllerOptiLC__L) {
        /* Find intermediate L */
        s_controller_opti_L_max_val = s_controller_opti_L_max_cand_val       = s_controller_opti_L_mid_val;
 
        /* New mid */
        s_controller_opti_L_mid_val = (s_controller_opti_L_min_val + s_controller_opti_L_mid_val) / 2.0f;

      } else {
        /* Find intermediate C */
        s_controller_opti_C_max_val = s_controller_opti_C_max_cand_val       = s_controller_opti_C_mid_val;
 
        /* New mid */
        s_controller_opti_C_mid_val = (s_controller_opti_C_min_val + s_controller_opti_C_mid_val) / 2.0f;
      }
    }
  }
}

static void controllerFSM_ZeroXHalfStrategy(void)
{
  if (s_controller_FSM_optiStrat != ControllerOptiStrat__Half) {
    return;
  }

  printf("controllerFSM_ZeroXHalfStrategy 1: L_max - L_min=%f\r\n", (s_controller_opti_L_max_val - s_controller_opti_L_min_val));

  /* Work out the half strategy */
  controllerFSM_HalfStrategy();

  if (s_controller_FSM_optiLC == ControllerOptiLC__L) {
    /* Find intermediate L */

    /* Check if minimum of SWR is found */
    if (Controller_Ls_nH[0] >= fabs(s_controller_opti_L_max_val - s_controller_opti_L_min_val)) {
      printf("controllerFSM_ZeroXHalfStrategy 2: L_max - L_min=%f\r\n", (s_controller_opti_L_max_val - s_controller_opti_L_min_val));
      /* Check if optimum found by increase of L */
      if (s_controller_opti_L_mid_val >= Controller_Ls_nH[0]) {
        /* Advance L, at least by one step, limiting */
        float advanced = s_controller_opti_L_mid_val * 1.5f + Controller_Ls_nH[0];
        if (advanced > 2.0f * Controller_Ls_nH[7]) {
          s_controller_opti_L_mid_val = controllerCalcMatcherNH2L( controllerCalcMatcherL2nH(advanced) );
        } else {
          s_controller_opti_L_mid_val = advanced;
        }

        /* Next optimize C */
        s_controller_opti_C_min_val = s_controller_opti_C_min_cand_val = Controller_C0_pF;
        s_controller_opti_min_swr   = s_controller_opti_min_cand_swr   = s_controller_opti_mid_swr;
        s_controller_opti_C_mid_val = Controller_C0_pF + Controller_Cs_pF[0];
        s_controller_opti_LCpongCtr = 0U;
        s_controller_FSM_optiLC     = ControllerOptiLC__C;
        s_controller_FSM_optiStrat  = ControllerOptiStrat__Double;
        s_controller_FSM_optiUpDn   = ControllerOptiUpDn__Up;
        s_controller_FSM_state      = ControllerFsm__findMinSwr;

        /* Forget this minimum due to C advance */
        s_controller_adc_swr        = 99.9f;

      } else {
        /* Switch over to opposite CVH constellation */
        controllerFSM_SwitchOverCVH();
      }
    }

  } else if (s_controller_FSM_optiLC == ControllerOptiLC__C) {
    /* Find intermediate C */

    /* Check if minimum of SWR is found */
    if (Controller_Cs_pF[0] >= fabs(s_controller_opti_C_max_val - s_controller_opti_C_min_val)) {
      /* Check if optimum will be found by increase of C */
      if (s_controller_opti_C_mid_val > Controller_Cs_pF[1]) {
        /* Advance C, at least by one step, limiting */
        float advanced = s_controller_opti_C_mid_val * 1.2f + Controller_Cs_pF[0];
        if (advanced > 2.0f * Controller_Cs_pF[7]) {
          s_controller_opti_C_mid_val = controllerCalcMatcherPF2C( controllerCalcMatcherC2pF(advanced) );
        } else {
          s_controller_opti_C_mid_val = advanced;
        }

        /* Next optimize L */
        s_controller_opti_L_min_val = s_controller_opti_L_min_cand_val = Controller_L0_nH;
        s_controller_opti_min_swr   = s_controller_opti_min_cand_swr   = s_controller_opti_mid_swr;
        s_controller_opti_L_mid_val = Controller_L0_nH + Controller_Ls_nH[0];
        s_controller_opti_LCpongCtr = 0U;
        s_controller_FSM_optiLC     = ControllerOptiLC__L;
        s_controller_FSM_optiStrat  = ControllerOptiStrat__Double;
        s_controller_FSM_optiUpDn   = ControllerOptiUpDn__Up;
        s_controller_FSM_state      = ControllerFsm__findMinSwr;

        /* Forget this minimum due to L advance */
        s_controller_adc_swr        = 99.9f;

      } else {
        /* Switch over to opposite CVH constellation */
        controllerFSM_SwitchOverCVH();
      }
    }
  }
}

static void controllerFSM_OptiHalfStrategy(void)
{
  if ((s_controller_FSM_optiLC    == ControllerOptiLC__L      ) &&
      (s_controller_FSM_optiStrat == ControllerOptiStrat__Half)) {
    /* Find intermediate L */
    controllerFSM_HalfStrategy();

    if (Controller_Ls_nH[0] >= (s_controller_opti_L_max_val - s_controller_opti_L_min_val)) {
      if (++s_controller_opti_LCpongCtr <= Controller_AutoSWR_LCpong_Max) {
        /* Optimize C, again */
        s_controller_FSM_optiLC     = ControllerOptiLC__C;
        s_controller_FSM_optiStrat  = (s_controller_opti_mid_swr < 1.5f) ?  ControllerOptiStrat__SingleCnt : ControllerOptiStrat__Double;
        s_controller_FSM_optiUpDn   = ControllerOptiUpDn__Up;
        s_controller_FSM_state      = ControllerFsm__findMinSwr;

      } else {
        /* Switch over to opposite CVH constellation */
        controllerFSM_SwitchOverCVH();
      }
    }

  } else if ((s_controller_FSM_optiLC    == ControllerOptiLC__C      ) &&
             (s_controller_FSM_optiStrat == ControllerOptiStrat__Half)) {
    /* Find intermediate C */
    controllerFSM_HalfStrategy();

    if (Controller_Cs_pF[0] >= (s_controller_opti_C_max_val - s_controller_opti_C_min_val)) {
      if (++s_controller_opti_LCpongCtr <= Controller_AutoSWR_LCpong_Max) {
        /* Optimize L, again */
        s_controller_FSM_optiLC     = ControllerOptiLC__L;
        s_controller_FSM_optiStrat  = (s_controller_opti_mid_swr < 1.5f) ?  ControllerOptiStrat__SingleCnt : ControllerOptiStrat__Double;
        s_controller_FSM_optiUpDn   = ControllerOptiUpDn__Up;
        s_controller_FSM_state      = ControllerFsm__findMinSwr;

      } else {
        /* Switch over to opposite CVH constellation */
        controllerFSM_SwitchOverCVH();
      }
    }
  }
}

static void controllerFSM(void)
{
  switch (s_controller_FSM_state)
  {

  case ControllerFsm__NOP:
  case ControllerFsm__doAdc:
  {
    /* Init SWR compare value */
    s_controller_last_swr = 99.9f;

    controllerFSM_StartAdc();

    s_controller_FSM_state = ControllerFsm__startAuto;
  }
    break;

  case ControllerFsm__startAuto:
  {
    /* Pull global vars */
    controllerFSM_GetGlobalVars();

    /* Check for security */
    if (controllerFSM_CheckPower()) {
      break;
    }

    /* Check if auto tuner should start */
    if (controllerFSM_CheckSwrTime()) {
      break;
    }

    /* Run (V)SWR optimization */
    s_controller_FSM_optiCVH      = ControllerOptiCVH__CV;
    s_controller_FSM_optiLC       = ControllerOptiLC__L;
    s_controller_FSM_optiStrat    = ControllerOptiStrat__Double;
    s_controller_FSM_optiUpDn     = ControllerOptiUpDn__Up;
    s_controller_FSM_state        = ControllerFsm__findImagZero;
    s_controller_opti_CVHpongCtr  = 0U;
    s_controller_opti_LCpongCtr   = 0U;
    s_controller_opti_L_min_val   = s_controller_opti_L_min_cand_val = Controller_L0_nH;
    s_controller_opti_L_mid_val   = Controller_L0_nH + Controller_Ls_nH[0];
    s_controller_opti_C_min_val   = s_controller_opti_C_min_cand_val = s_controller_opti_C_mid_val = Controller_C0_pF;
    s_controller_opti_min_swr     = s_controller_opti_min_cand_swr   = 99.9f;

    /* Logging */
    {
      char buf[128];

      const int len = sprintf(buf, "Controller FSM: ControllerFsm__startAuto - start auto tuner.\r\n");
      usbLogLen(buf, len);
    }

    /* Push opti data to relays */
    controllerFSM_PushOptiVars();
    controllerFSM_StartAdc();
  }
    break;

  case ControllerFsm__findImagZero:
  {
    /* Pull global vars */
    controllerFSM_GetGlobalVars();

    /* Check for security */
    if (controllerFSM_CheckPower()) {
      break;
    }

    /* Show current state of optimization */
    controllerFSM_LogState();

    /* Check for SWR */
    if (s_controller_opti_mid_swr <= s_controller_last_swr) {
      /* SWR got better */

      if (s_controller_opti_mid_swr <= Controller_AutoSWR_SWR_Max) {
        /* SWR: we have got it */
        controllerFSM_LogAutoFinished();
        break;
      }

      /* Handle limits */
      //ControllerFSM_HandleLimits(true);

    } else {
      /* SWR got worse */

      /* Handle limits */
      //ControllerFSM_HandleLimits(false);

      if (s_controller_FSM_optiStrat == ControllerOptiStrat__Double) {
        /* Change strategy */
        s_controller_FSM_optiStrat = ControllerOptiStrat__Half;
        s_controller_FSM_optiUpDn  = ControllerOptiUpDn__Dn;

      } else if (s_controller_FSM_optiStrat == ControllerOptiStrat__Half) {
        s_controller_FSM_optiUpDn  = !s_controller_FSM_optiUpDn;
      }
    }

    /* Execute the strategy */
    if (s_controller_FSM_optiStrat == ControllerOptiStrat__Double) {
      /* Double L/C for quick access */
      controllerFSM_DoubleStrategy();

    } else if (s_controller_FSM_optiStrat == ControllerOptiStrat__Half) {
      /* Half strategy for zero X configuration */
      controllerFSM_ZeroXHalfStrategy();
    }

    /* Push opti data to relays */
    controllerFSM_PushOptiVars();
    controllerFSM_StartAdc();
  }
    break;

  case ControllerFsm__findMinSwr:
  {
exit(0);
    /* Pull global vars */
    controllerFSM_GetGlobalVars();

    /* Check for security */
    if (controllerFSM_CheckPower())
      break;

    /* Show current state of optimization */
    controllerFSM_LogState();

    /* Check for SWR */
    if (s_controller_opti_mid_swr <= s_controller_last_swr) {
      /* SWR got better */

      if (s_controller_opti_mid_swr <= Controller_AutoSWR_SWR_Max) {
        /* SWR: we have got it */
        controllerFSM_LogAutoFinished();
        break;
      }

      /* Handle limits */
      //ControllerFSM_HandleLimits(true);

      /* Search strategy */
      if (s_controller_FSM_optiStrat == ControllerOptiStrat__Double) {
        /* Double C for quick access */
        controllerFSM_DoubleStrategy();

      } else if (s_controller_FSM_optiStrat == ControllerOptiStrat__SingleCnt) {
        if (s_controller_FSM_optiUpDn == ControllerOptiUpDn__Up) {
          /* Single step increase */
          /* Up direction */

          if (s_controller_FSM_optiLC == ControllerOptiLC__L) {
            /* Inductivity */
            s_controller_opti_L_mid_val += Controller_Ls_nH[0];
            if (s_controller_opti_L_mid_val >= 2.0f * Controller_Ls_nH[7]) {
              s_controller_opti_L_mid_val = controllerCalcMatcherL2nH( controllerCalcMatcherNH2L(s_controller_opti_L_mid_val) );

              /* Banging the limit - try opposite CVH setup */
              controllerFSM_SwitchOverCVH();
            }

          } else {
            /* Capacity */
            s_controller_opti_C_mid_val += Controller_Cs_pF[0];
            if (s_controller_opti_C_mid_val >= 2.0f * Controller_Cs_pF[7]) {
              s_controller_opti_C_mid_val = controllerCalcMatcherC2pF( controllerCalcMatcherPF2C(s_controller_opti_C_mid_val) );

              /* Banging the limit - try opposite CVH setup */
              controllerFSM_SwitchOverCVH();
            }
          }

        } else {
          /* Single step decrease */
          /* Down direction */

          if (s_controller_FSM_optiLC == ControllerOptiLC__L) {
            /* Inductivity */
            s_controller_opti_L_mid_val -= Controller_Ls_nH[0];
            if (s_controller_opti_L_mid_val < Controller_L0_nH) {
              s_controller_opti_L_mid_val = Controller_L0_nH;

              if (++s_controller_opti_LCpongCtr <= Controller_AutoSWR_LCpong_Max) {
                /* Change over to C trim */
                s_controller_FSM_optiLC     = ControllerOptiLC__C;
                s_controller_FSM_optiStrat  = (s_controller_opti_mid_swr < 1.5f) ?  ControllerOptiStrat__SingleCnt : ControllerOptiStrat__Double;

              } else {
                /* Exhausted - try opposite CVH setup */
                controllerFSM_SwitchOverCVH();
              }
            }

          } else {
            /* Capacity */
            s_controller_opti_C_mid_val -= Controller_Cs_pF[0];
            if (s_controller_opti_C_mid_val < Controller_C0_pF) {
              s_controller_opti_C_mid_val = Controller_C0_pF;

              if (++s_controller_opti_LCpongCtr <= Controller_AutoSWR_LCpong_Max) {
                /* Change over to L trim */
                s_controller_FSM_optiLC     = ControllerOptiLC__L;
                s_controller_FSM_optiStrat  = (s_controller_opti_mid_swr < 1.5f) ?  ControllerOptiStrat__SingleCnt : ControllerOptiStrat__Double;

              } else {
                /* Exhausted - try opposite CVH setup */
                controllerFSM_SwitchOverCVH();
              }
            }
          }
        }
      }

    } else {
      /* SWR got worse */

      /* Handle limits */
      //ControllerFSM_HandleLimits(false);

      /* Search strategy */
      if (s_controller_FSM_optiStrat == ControllerOptiStrat__Double) {
        /* Change strategy */
        s_controller_FSM_optiStrat  = ControllerOptiStrat__Half;
        s_controller_FSM_optiUpDn   = ControllerOptiUpDn__Dn;

      } else if (s_controller_FSM_optiStrat == ControllerOptiStrat__SingleCnt) {
        /* Change direction */
        s_controller_FSM_optiUpDn = !s_controller_FSM_optiUpDn;

        if (s_controller_FSM_optiUpDn == ControllerOptiUpDn__Up) {
          /* Single step increase */
          /* Up direction */

          if (++s_controller_opti_LCpongCtr <= Controller_AutoSWR_LCpong_Max) {
            /* Change over to opposite L/C component trim */
            s_controller_FSM_optiLC     = !s_controller_FSM_optiLC;
            s_controller_FSM_optiStrat  = (s_controller_opti_mid_swr < 1.5f) ?  ControllerOptiStrat__SingleCnt : ControllerOptiStrat__Double;

          } else {
            /* Switch over to opposite CVH constellation */
            controllerFSM_SwitchOverCVH();
          }

        } else {
          /* Single step decrease */
          /* Down direction */

          if (s_controller_FSM_optiLC == ControllerOptiLC__L) {
            /* Inductivity */
            s_controller_opti_L_mid_val -= Controller_Ls_nH[0];
            if (s_controller_opti_L_mid_val < Controller_L0_nH) {
              s_controller_opti_L_mid_val = Controller_L0_nH;

              if (++s_controller_opti_LCpongCtr <= Controller_AutoSWR_LCpong_Max) {
                /* Change over to C trim */
                s_controller_FSM_optiLC     = ControllerOptiLC__C;
                s_controller_FSM_optiStrat  = (s_controller_opti_mid_swr < 1.5f) ?  ControllerOptiStrat__SingleCnt : ControllerOptiStrat__Double;

              } else {
                /* Switch over to opposite CVH constellation */
                controllerFSM_SwitchOverCVH();
              }
            }

          } else {
            /* Capacity */
            s_controller_opti_C_mid_val -= Controller_Cs_pF[0];
            if (s_controller_opti_C_mid_val < Controller_C0_pF) {
              s_controller_opti_C_mid_val = Controller_C0_pF;

              if (++s_controller_opti_LCpongCtr <= Controller_AutoSWR_LCpong_Max) {
                /* Change over to L trim */
                s_controller_FSM_optiLC     = ControllerOptiLC__L;
                s_controller_FSM_optiStrat  = (s_controller_opti_mid_swr < 1.5f) ?  ControllerOptiStrat__SingleCnt : ControllerOptiStrat__Double;

              } else {
                /* Switch over to opposite CVH constellation */
                controllerFSM_SwitchOverCVH();
              }
            }
          }
        }
      }
    }

    /* Half strategy (when active) */
    controllerFSM_OptiHalfStrategy();

    /* Push opti data to relays */
    controllerFSM_PushOptiVars();
    controllerFSM_StartAdc();
  }
    break;

  case ControllerFsm__done:
  {
    exit(0);

    /* Done - wait for new start */
    s_controller_FSM_state = ControllerFsm__doAdc;
    controllerFSM_StartAdc();
  }
    break;

  default:
  {
    s_controller_FSM_state = ControllerFsm__NOP;
  }

  }  // switch ()
}

/* Cyclic job to do */
void controllerCyclicTimerEvent(void)
{
  uint32_t  msgAry[16];
  uint8_t   msgLen = 0U;

  /* FSM logic */
  controllerFSM();
  printf("TimerEvent: s_controller_FSM_state= %d\r\n", s_controller_FSM_state);

  if (s_controller_doAdc) {
    /* Get ADC channels */
    msgAry[msgLen++]  = controllerCalcMsgHdr(Destinations__Rtos_Default, Destinations__Controller, 0U, MsgDefault__CallFunc01_MCU_ADC1);
    msgAry[msgLen++]  = controllerCalcMsgHdr(Destinations__Rtos_Default, Destinations__Controller, 0U, MsgDefault__CallFunc02_MCU_ADC3_VDIODE);
    msgAry[msgLen++]  = controllerCalcMsgHdr(Destinations__Rtos_Default, Destinations__Controller, 0U, MsgDefault__CallFunc03_MCU_ADC2_FWD);
    msgAry[msgLen++]  = controllerCalcMsgHdr(Destinations__Rtos_Default, Destinations__Controller, 0U, MsgDefault__CallFunc04_MCU_ADC2_REV);
  }

  /* Push to queue */
  //controllerMsgPushToInQueue(msgLen, msgAry, 1UL);
  __asm volatile("nop");
}

void controllerInit(void)
{
  /* Set relay state */
  controllerFSM_PushOptiVars();

  /* Reset SWR start timer */
  s_controller_swr_tmr = osKernelSysTick();
}
